AssistiveLabs/SynthSense/app/map.png

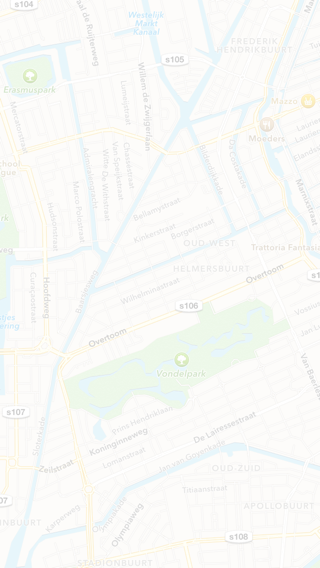
app/map.png
