AssistiveLabs/SynthSense/app/microphone.png

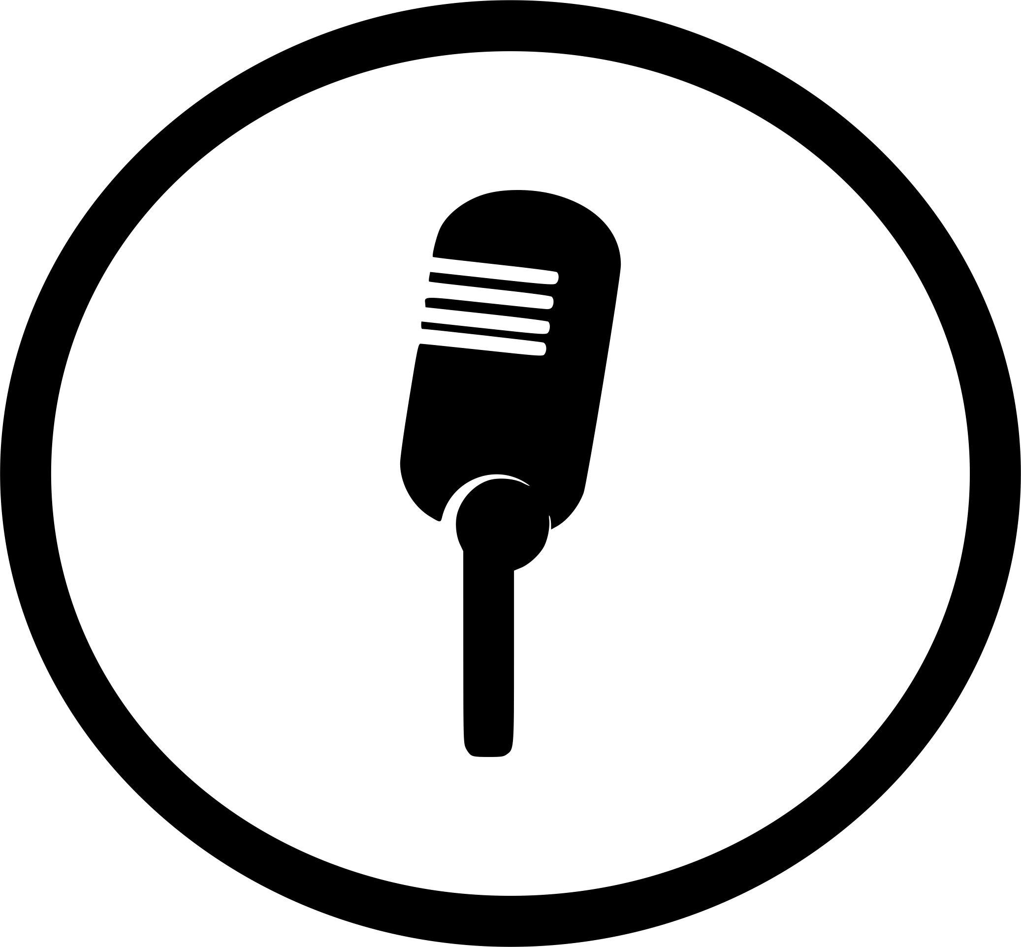
app/microphone.png
