AssistiveLabs/SynthSense/images/App1.png

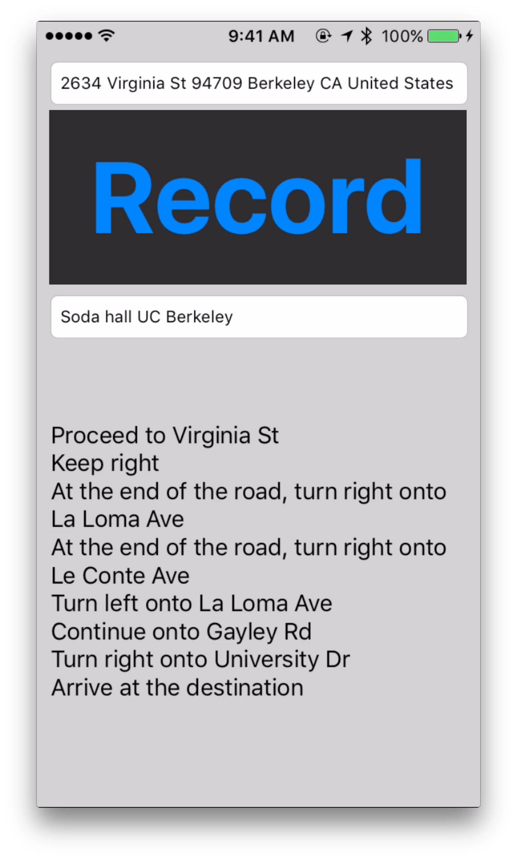
images/App1.png
