AssistiveLabs/SynthSense/images/Handle1.jpg

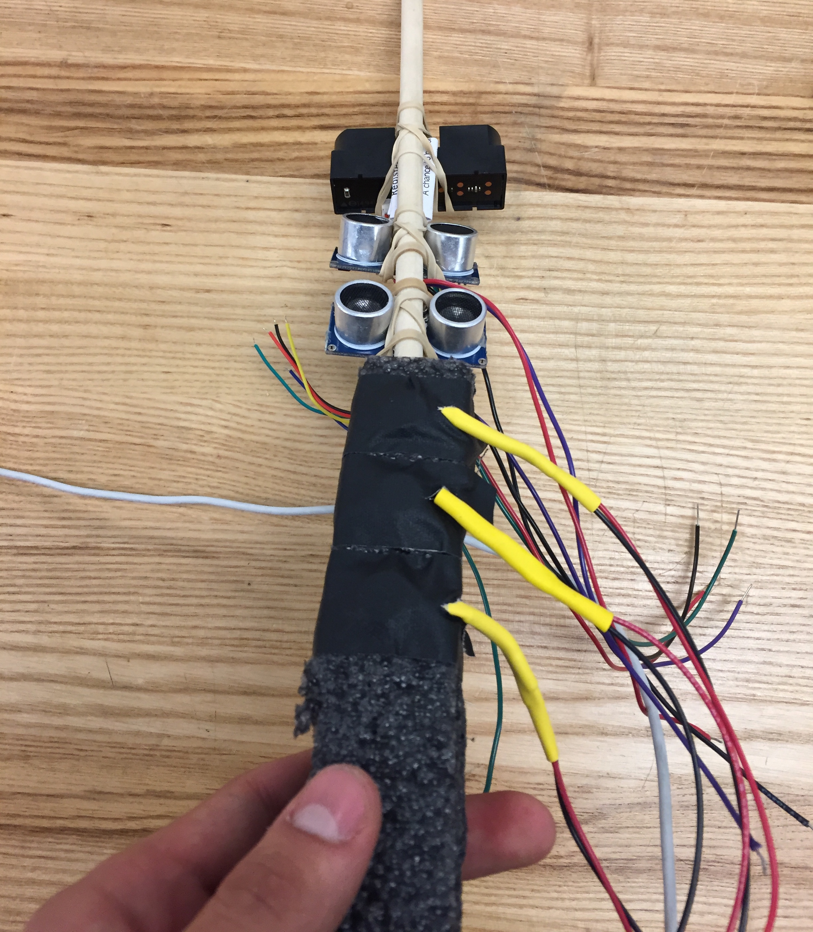
images/Handle1.jpg
