AssistiveLabs/SynthSense/images/Handle3.png

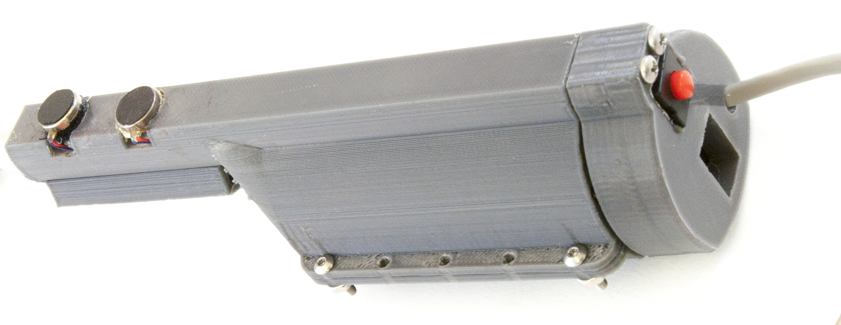
images/Handle3.png
