AssistiveLabs/SynthSense/images/Navband1.PNG

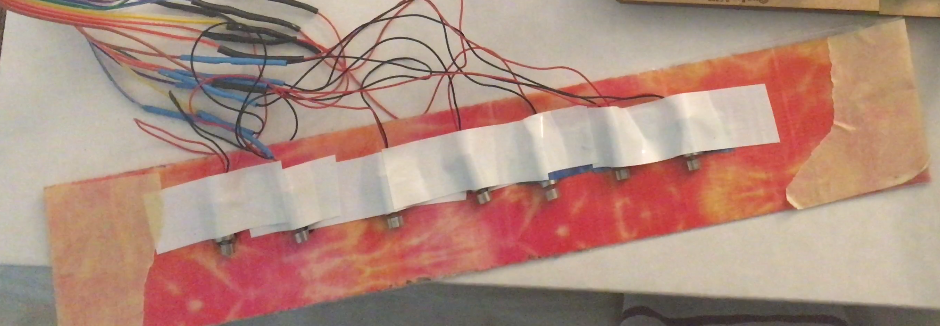
images/Navband1.PNG
