AssistiveLabs/SynthSense/images/Navband2.png

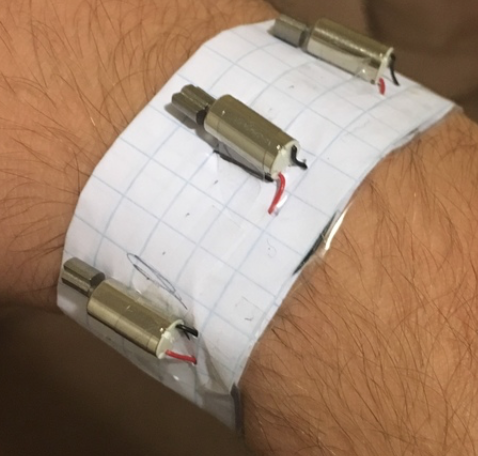
images/Navband2.png
