AssistiveLabs/SynthSense/images/Navband4.png

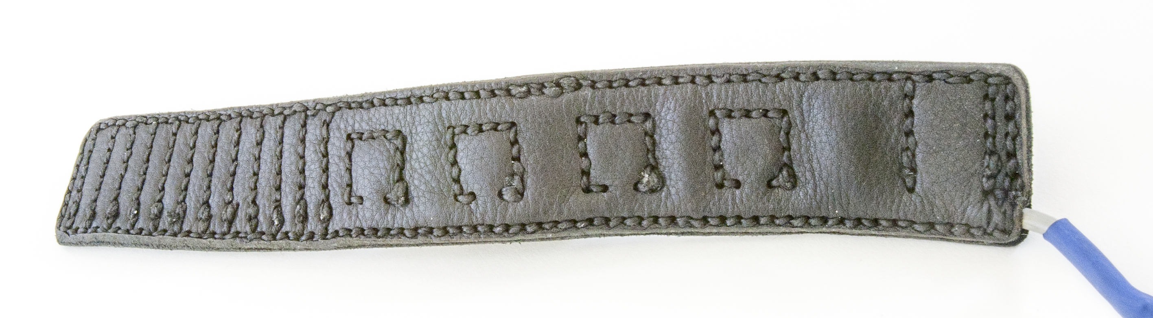
images/Navband4.png
