AssistiveLabs/SynthSense/images/Sensor2.JPG

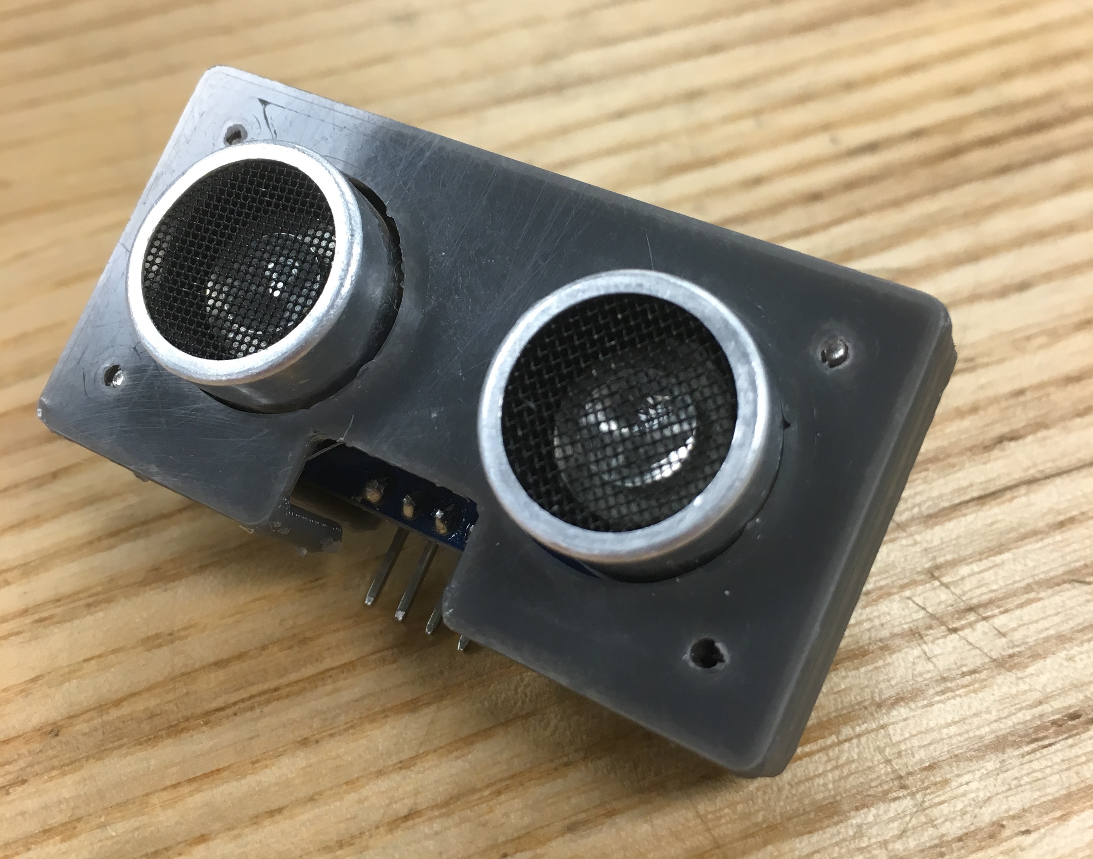
images/Sensor2.JPG
