AssistiveLabs/SynthSense/images/Sensor3.png

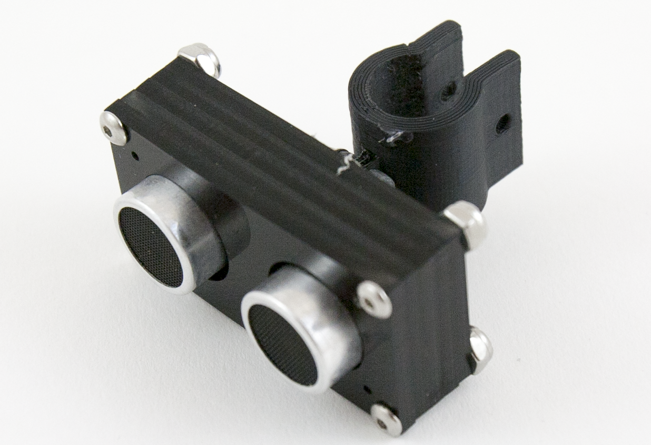
images/Sensor3.png
